GreenShoeGarage/Centerpoint_LightsAndSounds/Documentation/Photos/AdapterPCB_Bottom.png

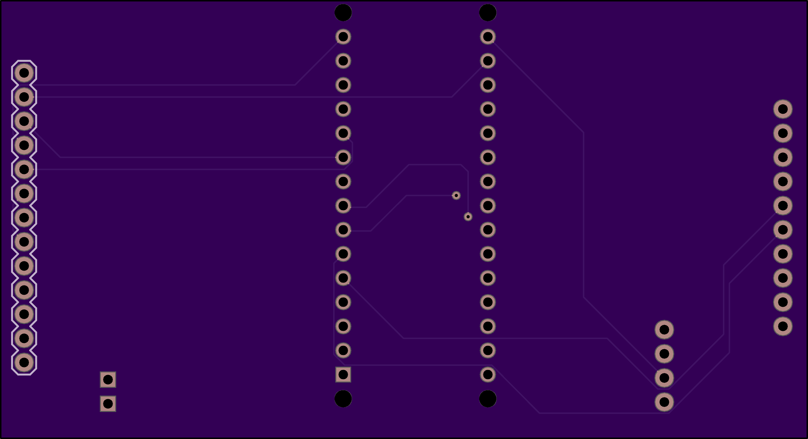
Documentation/Photos/AdapterPCB_Bottom.png
