GreenShoeGarage/Centerpoint_LightsAndSounds/Documentation/Photos/Keypad_Enclosure.jpg

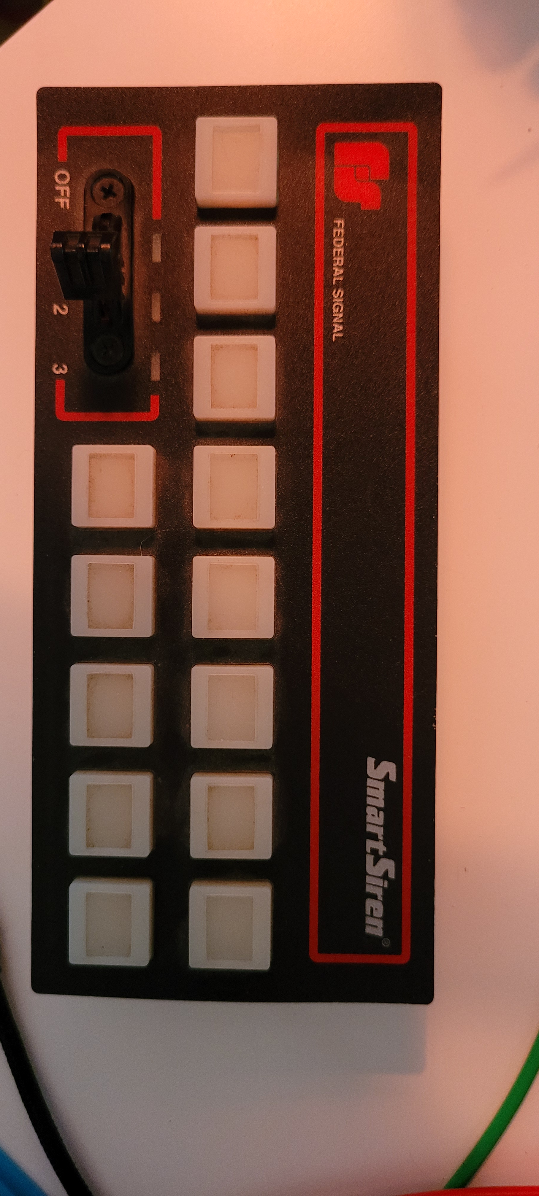
Documentation/Photos/Keypad_Enclosure.jpg
