GreenShoeGarage/Centerpoint_LightsAndSounds/Documentation/Photos/Keypad_PCB_EDITED (Medium).png

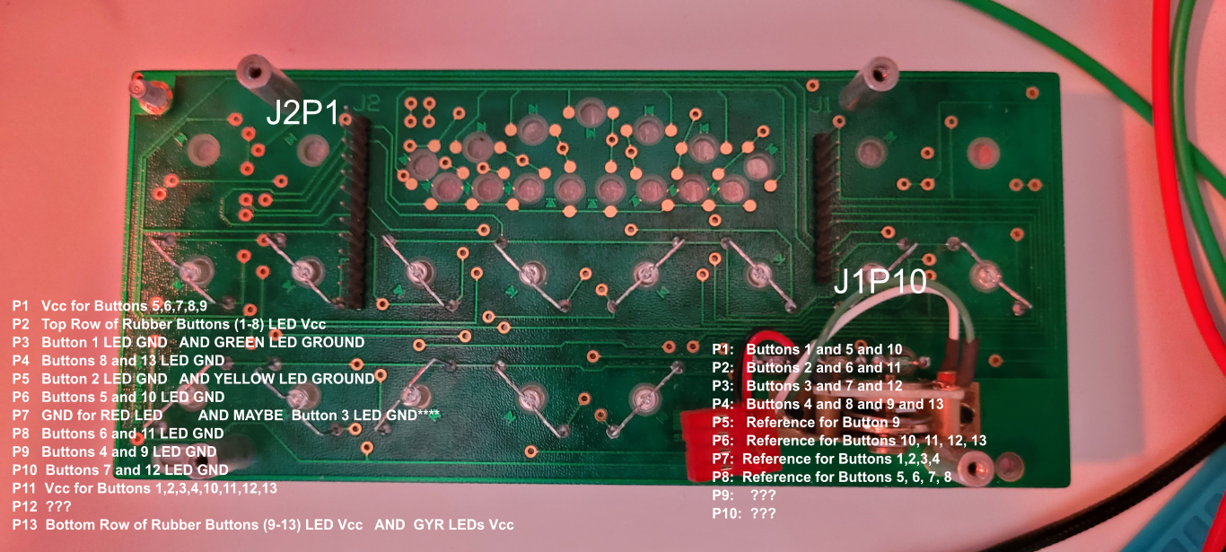
Documentation/Photos/Keypad_PCB_EDITED (Medium).png
