GreenShoeGarage/Centerpoint_LightsAndSounds/Documentation/Photos/Keypad_PCB_RAW.jpg

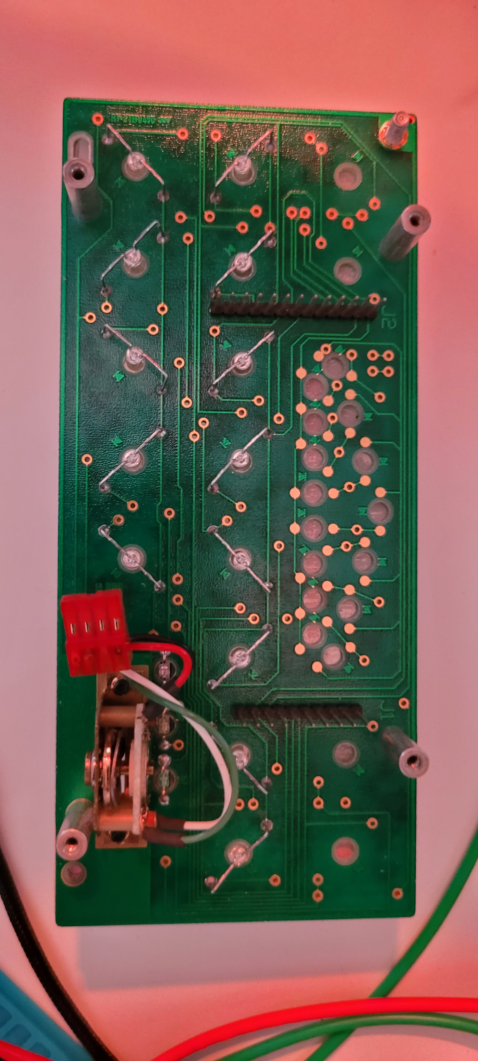
Documentation/Photos/Keypad_PCB_RAW.jpg
