GreenShoeGarage/Centerpoint_LightsAndSounds/Documentation/Photos/Logic_PCB.jpg

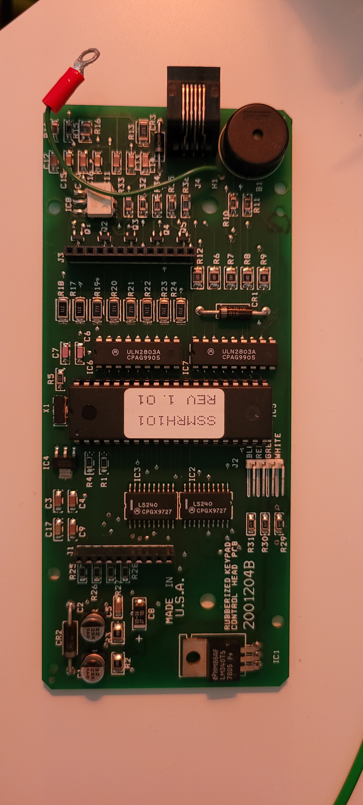
Documentation/Photos/Logic_PCB.jpg
