GreenShoeGarage/Centerpoint_LightsAndSounds/Documentation/Photos/OSHPark_PCBOrder.png

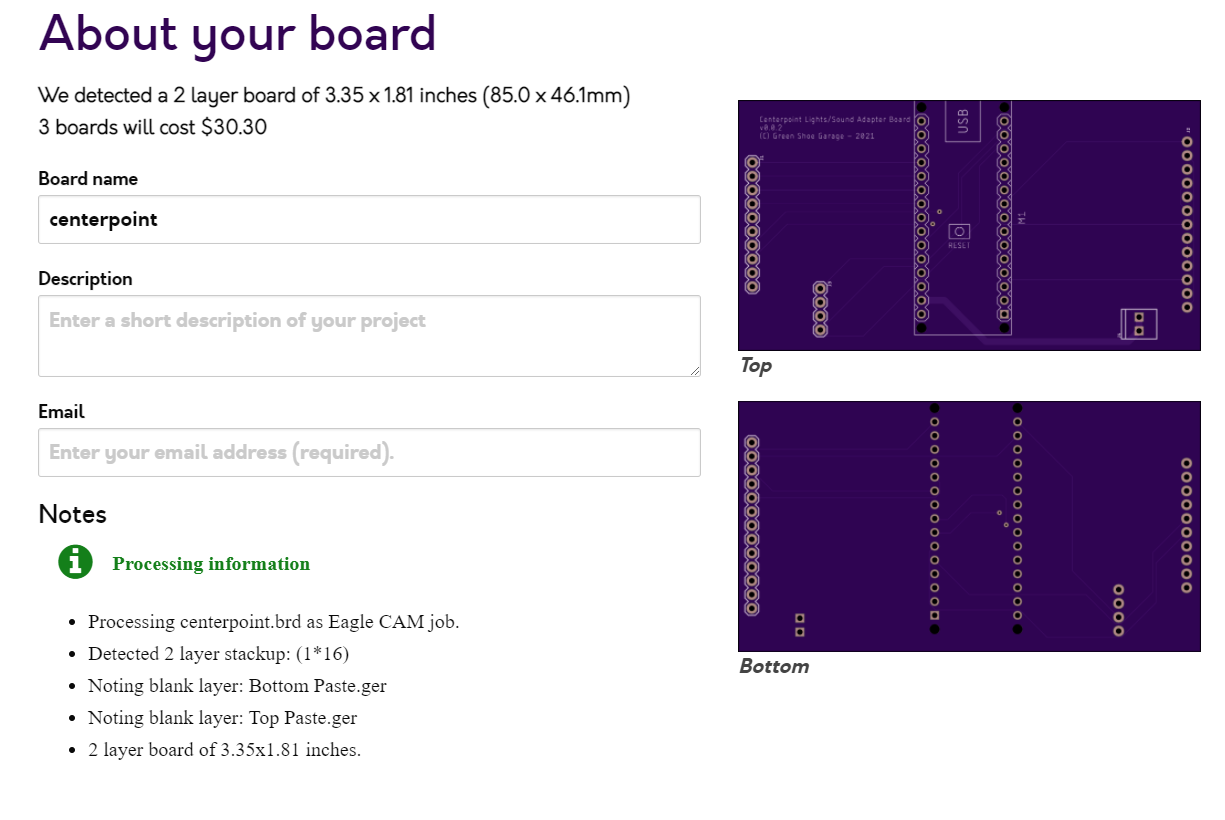
Documentation/Photos/OSHPark_PCBOrder.png
