GreenShoeGarage/Centerpoint_LightsAndSounds/Documentation/Photos/PCB_3DRender.jpg

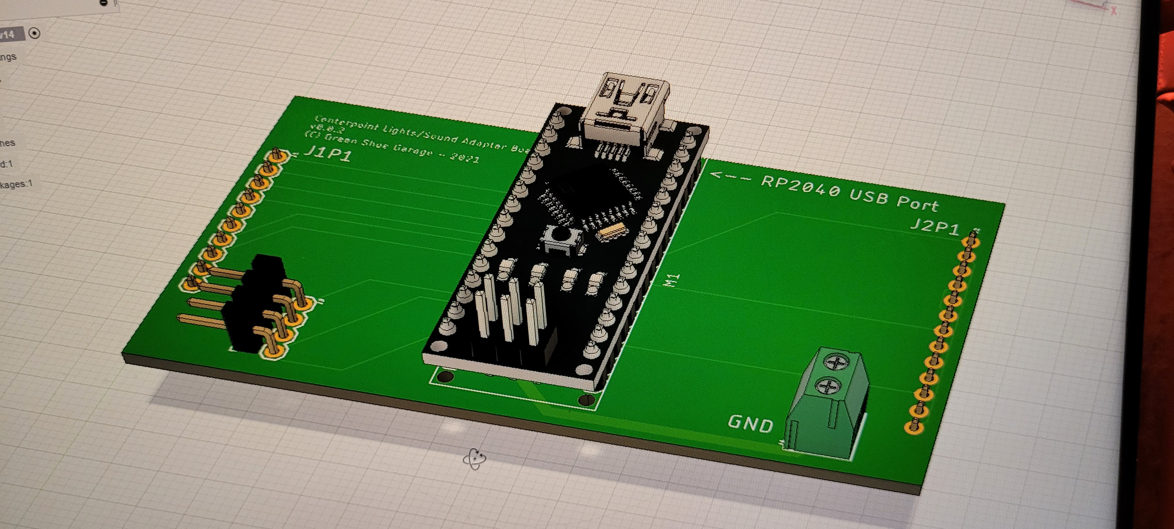
Documentation/Photos/PCB_3DRender.jpg
